bytesizedengineering/PCB-tile-based-game/mechanical design/diffuser OOO.3mf

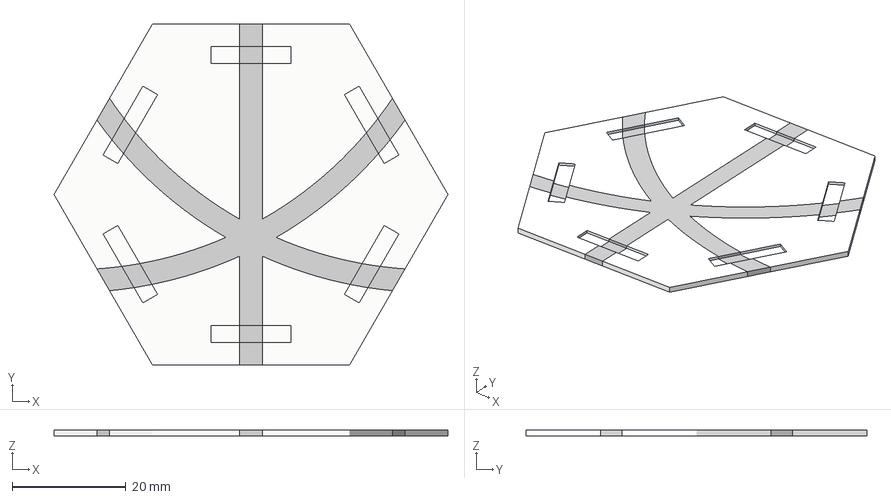
[picture p14: CAD file, 2025-06-16]
mechanical design/diffuser OOO.3mf
69.3 x 60.0 x 1.00 mm
diffuser (1)
diffuser (2)
diffuser (3)
diffuser (4)
diffuser (5)
diffuser
